arjunven/STM32_Nixie/simulation/Reset Button/Reset.asc

C1: Cap; 10µ
C2: Cap; 100n
D1: Diode
M1: nmos; 2N7002
R1: Res; 1k
R2: Res; 1Meg
R3: Res; 55k
R4: Res; 10k
R5: Res; 100
R6: Res; 200k
S1: sw
V1: Voltage; 3.3V
V2: Voltage; PULSE(0 1 1 1p 1p 0.75 2 2); Rser=10
V3: Voltage; PULSE(0 1 40 1p 1p 5 5 1); Rser=10
V4: Voltage; 1.164
V5: Voltage; 1.833
Named nets: 0, SW_CTLR, nRST, BOOT0, gate, logic_LO, logic_HI
.MODEL MY_SW SW(Ron=112m Roff=1Meg Vt=0.5 Vh=-0.1)
.tran 60
Quick Press to Reset
Long press for bootloader
