arjunven/STM32_Nixie/simulation/Reset Button/Reset_moonlander.asc

C1: Cap; 16µ
C2: Cap; 80n
D1: Diode
M1: nmos; 2N7002
R1: Res; 4.7k
R2: Res; 30k
R3: Res; 50k
R4: Res; 100k
S1: sw
V1: Voltage; 3.3V
V2: Voltage; PULSE(0 1 1 1p 1p 0.5 5 2)
Named nets: 0, SW_CTLR, nRST, BOOT0, gate
.MODEL MY_SW SW(Ron=112m Roff=1Meg Vt=0.5 Vh=-0.1)
.tran 10
