arjunven/STM32_Nixie/simulation/Generic Boost/180V_DCM_boost_parasitics_snub.asc

C1: Cap; {Cp}
C2: Cap; 138µF
C3: Cap; {Cout}
C4: Cap; {Cp}
C5: Cap; {Cs1}
C6: Cap; {Cs2}
D1: Diode
L1: ind; {L}
L2: ind; {Lp}
L3: ind; {Lp}
L4: ind; {Lp}
L5: ind; {Lp}
L6: ind; {Lp}
R1: Res; 9k
R2: Res; {Rs1}
R3: Res; {Rs2}
S1: sw
V1: Voltage; {Vin}; Rser=10m
V2: Voltage; PULSE(0 1 0 1p 1p {D/Fs} {Ts})
Named nets: 0, SW_CTLR, Vout, Vin, Vsw
.MODEL MY_SW SW(Ron=112m Roff=1Meg Vt=0.5 Vh=-0.1)
.PARAM L=3.3uH Cout=1uF Vout=180 Vin=5 Iout=20m Fs=351.6k Ts={1/Fs}
.tran .1m
.param D = sqrt((Iout*2*L*(Vout-Vin))/Ts)/Vin
DCM Duty Cycle
.ic V(Vout) = 174.49
.ic I(L1) = 1.5
.param Rs1=20
.step param Rs2 list 0.001m 10 20 30
.step param Cs2 list 50p 100p 150p
.param Rs2=20
.param Cs2=50p
.step param Rs1 list 0.001m 5 10 20 30
.param Cs1=50p
.step param Cs1 list 25p 50p 100p 150p
.param Cp=5p
.step param Cp list 1p 5p
.param Lp=1n
.step param Lp list 1p 5n
