arjunven/STM32_Nixie/simulation/180V_Boost_LM5156/180V_boost_LM5156.asc

C1: Cap; 3300pF
C2: Cap; 0.47µF
C3: Cap; 140µF
C4: Cap; 0.01µF
C5: Cap; 1300pF
C6: Cap; 0.1pF
C7: Cap; 1µF
D1: Diode
L1: ind; 3.3µ
R1: Res; 61.9k
R2: Res; 30m
R3: Res; 100
R4: Res; 499k
R5: Res; 2.8k
R6: Res; 69.8k
R7: Res; 32.4k
R8: Res; 9k
R9: Res; 69.8k
U1: LM5156-Q1_TRANS
U2: NMOS_TPH1110FNH_G0_00
V1: Voltage; 12; Rser=1m
Named nets: 0, Vo, SW, Vin, Vcc
.inc /Users/arjun/source/STM32_Nixie/simulation/180V_Boost_LM5156/TPH1110FNH_G0_00_LTspice_rev1.lib
.tran 30ms
