arjunven/STM32_Nixie/simulation/180V_cp_mult_boost/cp_mult_boost.asc

C1: Cap; 1.6µ
C2: Cap; 7.14µ
C3: Cap; 1µ
C4: Cap; 1µ
D1: Diode
D2: Diode
L1: Ind
R1: Res; 200
R2: Res; 1.8k
S1: sw
V1: Voltage; 5; Rser=1m
Named nets: 0, out, in, sw, cp_out1
.tran 12m
.step param X list 10u 20u
