arjunven/STM32_Nixie/simulation/180V_CP_mult_boost_TLV61046A/cp_mult_boost_TLV61046A.asc

C1: Cap; 1.6µ
C2: Cap; 7.14µ
C3: Cap; 1µ
C4: Cap; 1µ
D1: Diode
D2: Diode
R1: Res; 200
R2: Res; 1.8k
U1: TLV61046A_TRANS
U2: LSXND5050YKL220MMG
V1: Voltage; 5; Rser=1m
Named nets: 0, out, in, sw, cp_out1
.tran 12m
.step param X list 10u 20u
.inc TLV61046A_TRANS.lib
NRS5040T220MMGK spice model
22uH
