arjunven/STM32_Nixie/simulation/180V_CP_mult_boost_TLV61046A/LSXND5050YKL220MMG_LT.cir

* LTspice Encrypted File
* 
* This encrypted file has been supplied by a 3rd
* party vendor that does not wish to publicize
* the technology used to implement this library.
* 
* Permission is granted to use this file for
* simulations but not to reverse engineer its
* contents.
* 
* LSXND5050YKL220MMG     LTspice Model  ( Temperature / DC Bias Model )
*--------------------------------------------------------------------------------------------------------
* Model Generated by TAIYO YUDEN Corporation (http://www.ty-top.com)
* Version 1.0
* TAIYO YUDEN Control No. 44286.4445949074
* Copyright(c) 2021 TAIYO YUDEN CO.,LTD. All Rights Reserved.
*--------------------------------------------------------------------------------------------------------
* Product Description (link to TY-COMPAS)
* https://ds.yuden.co.jp/TYCOMPAS/or/detail?pn=LSXND5050YKL220MMG&u=M
*--------------------------------------------------------------------------------------------------------
* 
* Begin:
 D6 BC 38 CF 12 66 A4 A3 9B 7E 61 3A A2 57 1C 6E
 22 1E 89 CB 66 C8 71 2D EF E7 08 7E E7 15 57 A1
 0B 83 FF FE A7 14 21 95 B1 BB E7 0C 11 0E 85 4F
 0C 6B A1 CD 91 DA 8A 1C 80 A8 88 0C 2E E9 84 E5
 5E B7 F6 60 00 2E 1B 7D D2 B5 61 36 3E 01 95 5A
 24 0E 58 FC 2D 3F 7B E8 49 FB F9 79 E5 51 20 24
 72 1A 26 B1 C1 E6 75 75 D2 4C E4 BD 14 4F D3 D5
 D6 E8 24 13 D6 F6 60 0F A1 0D 72 7A 7D F1 B6 26
 B7 BA 56 6A D5 71 B7 EF A0 10 77 24 9C 2B E7 37
 14 5D 4A 04 13 4F 0B 91 8A 3D B0 10 CA D1 88 B6
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
 D4 41 13 82 1B 6E 81 04 94 0E 99 E9 DB 36 9F 2B
 A4 97 37 FA 0D C4 A5 E2 9B 38 57 18 67 F2 5E A1
 E3 D9 12 E7 23 4C 4D AF 7C 3B 89 78 C2 29 9D 86
 E2 8F 43 62 9D 59 AF 16 39 3B 97 96 1F 0B 55 82
 C2 7C 30 1A 8A 70 D1 76 20 52 D7 51 0D 73 34 22
 D2 52 E3 DF 71 7E 86 D5 8D AE B4 51 B9 96 91 66
 91 CF 72 9A C4 4E 7D EF CB A2 08 EA E1 16 38 01
 4B AD CC 88 93 01 D3 E3 A8 93 FC 0D 22 08 99 C6
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
