arjunven/STM32_Nixie/firmware/Core/Src/rtc.c

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
/* Includes ------------------------------------------------------------------*/
#include "rtc.h"

RTC_HandleTypeDef hrtc;

/* RTC init function */
void MX_RTC_Init(void)
{

  RTC_TimeTypeDef sTime = {0};
  RTC_DateTypeDef DateToUpdate = {0};

  /** Initialize RTC Only
  */
  hrtc.Instance = RTC;
  hrtc.Init.AsynchPrediv = RTC_AUTO_1_SECOND;
  hrtc.Init.OutPut = RTC_OUTPUTSOURCE_CALIBCLOCK;
  if (HAL_RTC_Init(&hrtc) != HAL_OK)
  {
    Error_Handler();
  }

  /* USER CODE BEGIN Check_RTC_BKUP */
    // clag-format on

  // Check if RTC is already running by checking the magic number in the backup
  if (BKP->DR1 == 0x32F2) {
    // RTC is already running, no need to initialize it
    return;
  }

  // clang-format off
  /* USER CODE END Check_RTC_BKUP */

  /** Initialize RTC and set the Time and Date
  */
  sTime.Hours = 0x0;
  sTime.Minutes = 0x0;
  sTime.Seconds = 0x0;

  if (HAL_RTC_SetTime(&hrtc, &sTime, RTC_FORMAT_BCD) != HAL_OK)
  {
    Error_Handler();
  }
  DateToUpdate.WeekDay = RTC_WEEKDAY_MONDAY;
  DateToUpdate.Month = RTC_MONTH_JANUARY;
  DateToUpdate.Date = 0x1;
  DateToUpdate.Year = 0x0;

  if (HAL_RTC_SetDate(&hrtc, &DateToUpdate, RTC_FORMAT_BCD) != HAL_OK)
  {
    Error_Handler();
  }
  /* USER CODE BEGIN RTC_Init 2 */
  // clang-format on

  // Magic number to indicate RTC has been initialized
  BKP->DR1 = 0x32F2;

  // clang-format off
  /* USER CODE END RTC_Init 2 */

}

void HAL_RTC_MspInit(RTC_HandleTypeDef* rtcHandle)
{

  if(rtcHandle->Instance==RTC)
  {
    HAL_PWR_EnableBkUpAccess();
    /* Enable BKP CLK enable for backup registers */
    __HAL_RCC_BKP_CLK_ENABLE();
    /* RTC clock enable */
    __HAL_RCC_RTC_ENABLE();
  }
}

void HAL_RTC_MspDeInit(RTC_HandleTypeDef* rtcHandle)
{

  if(rtcHandle->Instance==RTC)
  {
    /* Peripheral clock disable */
    __HAL_RCC_RTC_DISABLE();
  }
}
